theapi/solar/Mk3/stm32/lora_sensor/Inc/battery.h

#ifndef __battery_H
#define __battery_H
#ifdef __cplusplus
 extern "C" {
#endif

#include "stm32l0xx_hal.h"
#include "main.h"
#include "stdint.h"

 /**
  * Volts meassured for the battery.
  */
 uint16_t BATTERY_vcc();

 /**
  * Millivolts on the battery due to charging.
  */
 uint16_t BATTERY_ChargeMv();

 /**
  * Current into the battery due to charging.
  */
 int16_t BATTERY_ChargeMa();


#ifdef __cplusplus
}
#endif
#endif /*__battery_H */
